mdekrey/raspberry-BB8/scad/my-bb8-glue-bracket.scad

include <my-bb8-config.scad>;

rotate([180, 0, 0])
translate([0,0, panelHeight - radius])
panelGlueBracket();
