mdekrey/raspberry-BB8/scad/my-bb8-overview.scad

include <my-bb8-config.scad>;

bodySphere();
head();
