mdekrey/raspberry-BB8/scad/my-bb8-panel-1.scad

include <my-bb8-config.scad>;

panel = 1;
translate([0,0, panelHeight - radius])
{
    toolPanel(panel);

    if ($preview) {
        panelRingQuarter(false);
    }
}
