mdekrey/raspberry-BB8/scad/my-bb8-panel-2.scad

include <my-bb8-config.scad>;

panel = 2;
translate([0,0, panelHeight - radius])
toolPanel(panel);
