mdekrey/raspberry-BB8/scad/my-bb8-panel-3.scad

include <my-bb8-config.scad>;

panel = 3;
translate([0,0, panelHeight - radius])
toolPanel(panel);
