mdekrey/raspberry-BB8/scad/my-bb8-panel-6.scad

include <my-bb8-config.scad>;

panel = 6;
translate([0,0, panelHeight - radius])
toolPanel(panel);
