mdekrey/raspberry-BB8/scad/my-bb8-ring-quarter.scad

include <my-bb8-config.scad>;

translate([0,0, panelHeight - radius])
panelRingQuarter(false);
