mdekrey/raspberry-BB8/scad/my-bb8-triangle-third.scad

include <my-bb8-config.scad>;

tFrameThird();
