mdekrey/raspberry-BB8/scad/my-bb8-triangle.scad

include <my-bb8-config.scad>;

echo("print dimensions: ");
echo(x = (cos(35) * radius), y = (cos(35) * radius), z = (cos(35) * radius));
tFrameTriangle();
