mdekrey/raspberry-BB8/scad/shared.scad

panelDegrees = 35; // https://rimstar.org/science_electronics_projects/bb-8_dimensions.htm
panelRadius = radius * sin(panelDegrees);
insertionTolerance = 0.3;

visibleBoltHole = 4 / 2;
visibleBoltOuterRadius = radius * 0.07734 / 2;
visibleBoltCoverRadius = visibleBoltOuterRadius / 2;
visibleBoltBezelDepth = visibleBoltOuterRadius * 0.2;
visibleBoltBezel = visibleBoltOuterRadius * 0.2;

panelRingDegrees = panelDegrees * 4/15;
panelRingInnerDegrees = panelDegrees - panelRingDegrees;
panelRingInnerRadius = radius * sin(panelRingInnerDegrees);
panelRingOuterOverlap = 3;
panelRingInnerOverlap = 1;
panelArmDegrees = panelDegrees * 0.6;
panelArmBoltDegrees = panelDegrees * 0.52;

if (camlockBoltRadius * 2 + 2 > camlockNutThickness)
    warn("Camlock Bolt/Nut sizes invalid");

panelLockBoltDegrees = 90/ringLocksPerQuadrant;
panelRadiusOffset = radius * cos(panelDegrees);
rotateLockDegrees = panelLockBoltDegrees * 0.6; // The number of degrees to rotate the lock
panelRotateLockOffset = (panelLockBoltDegrees - rotateLockDegrees) / 2; // The number of degrees offset from the start position for the initial lock

panelRingInnerActualDegrees = asin((panelRingInnerRadius - insertionTolerance) / radius);
panelRingInnerInternalDegrees = asin((panelRingInnerRadius + panelRingInnerOverlap - insertionTolerance)
    / (radius - wallThickness));
panelHeight = radius - cos(panelRingInnerInternalDegrees) * (radius - wallThickness);
ringThickness = cos(panelRingInnerActualDegrees) * radius - cos(panelRingInnerInternalDegrees) * (radius - wallThickness) - 0.8;

panelDesignDepth = radius - cos(asin((panelRingInnerRadius * 0.92) / radius)) * radius + insertionTolerance;
panelDesignRadius = wallThickness - 0.2 * millisPerInch;

headRadius = radius * 295/506;
headBaseHeight = 20 * headRadius / 147.5;
headConeHeight = 20 * headRadius / 147.5;
headConeRadius = 111.5 * headRadius / 147.5;
headOffset = cos(asin(headConeRadius / radius)) * radius;

module bodySphere(additionalWallThickness = 0) {
    difference() {
        sphere(radius, $fn=$fnBody);
        sphere(radius - wallThickness - additionalWallThickness, $fn=$fn);
    };
}

module panelRing() {
    intersection() {
        bodySphere(additionalWallThickness = cos(panelDegrees) * maxLip);

        difference() {
            union() {
                translate([0,0, (radius) * cos(panelDegrees) - wallThickness])
                cylinder(r=panelRadius - insertionTolerance - panelRingOuterOverlap, h=radius * 2);
                translate([0,0,radius + cos(panelDegrees) * radius])
                cube([(panelRadius - insertionTolerance + panelRingOuterOverlap) * 2, (panelRadius - insertionTolerance + panelRingOuterOverlap) * 2, radius * 2], center=true);
            }
            difference() {
                cylinder(r=panelRingInnerRadius, h=radius * 2);

                linear_extrude(height=radius)
                panelX();
            }

            intersection() {
                sphere(radius - wallThickness/2+insertionTolerance, $fn=$fn);
                cylinder(r=panelRingInnerRadius + panelRingInnerOverlap + insertionTolerance, h=radius);
            }
        }
    }

}

panelAdditionalWallThickness = 0; // cos(panelDegrees) * maxLip;
panelInnerWall = radius - wallThickness - panelAdditionalWallThickness;
panelLayerWall = radius - (radius - panelInnerWall) * 0.6;

module panelX(offset = 0) {
    for (arm=[0:90:359]) {
        rotate([0,0,arm+45])
        translate([-83, 83, 0])
        offset(r=offset)
        import("panel-x.svg", center=true, dpi=2611.8439045872/panelRingInnerRadius);
    }
}

module panel() {
    difference() {
        intersection() {
            bodySphere(additionalWallThickness = panelAdditionalWallThickness);

            union() {
                intersection() {
                    cylinder(r=panelRingInnerRadius - insertionTolerance, h=radius * 2);

                    difference() {
                        cube([radius*2,radius*2,radius*2], center=true);
                        sphere(radius - wallThickness/2 - insertionTolerance, $fn=$fn);

                        linear_extrude(height=radius)
                        panelX(offset=insertionTolerance);
                    }
                }

                intersection() {
                    sphere(radius - wallThickness/2 - insertionTolerance, $fn=$fn);
                    cylinder(r=panelRingInnerRadius + panelRingInnerOverlap - insertionTolerance, h=radius);
                }
            }

        }

        difference() {
            children();
            sphere(r=1);

            sphere(r=radius - panelDesignRadius, $fn=$fnDetail);
        }

        for (i = [0 : 90 : 360]) {
            rotate([0, panelArmBoltDegrees, i])
            translate([0, 0, radius - wallThickness - panelAdditionalWallThickness])
            rotate([0, 180, 0])
            visibleBoltHole();
        }
    }
}

module panelMain() {
    difference() {
        panel() children();

        if (smallPrintBed) {
            translate([
                0, 0,
                radius * 2 - panelHeight + ringThickness])
            rotate([0,0,90 + 20])
            translate([- insertionTolerance / 2, 0, 0])
            cube([insertionTolerance, radius*2, radius*2], center=true);
        }

        translate([
            0, 0,
            radius - panelHeight + ringThickness - insertionTolerance / 2])
        cube([radius*2, radius*2, insertionTolerance], center=true);


        if (smallPrintBed) {
            translate([
                0, 0,
                -panelHeight + ringThickness])
            linear_extrude(height=radius)
            for (i = [45,180 + 45])
            rotate([0,0,i])
            polygon([
                [+insertionTolerance / 2, +(panelRingInnerRadius + panelRingInnerOverlap)],
                [+insertionTolerance / 2, +(panelRingInnerRadius + panelRingInnerOverlap - 5)],
                [+insertionTolerance / 2 + 5, +(panelRingInnerRadius + panelRingInnerOverlap - 5)],
                [+insertionTolerance / 2 + 5, +(panelRingInnerRadius + panelRingInnerOverlap - 10)],
                [+insertionTolerance / 2, +(panelRingInnerRadius + panelRingInnerOverlap - 10)],
                [+insertionTolerance / 2, 0],
                [-insertionTolerance / 2, 0],
                [-insertionTolerance / 2, +(panelRingInnerRadius + panelRingInnerOverlap - 10 + insertionTolerance)],
                [-insertionTolerance / 2 + 5, +(panelRingInnerRadius + panelRingInnerOverlap - 10 + insertionTolerance)],
                [-insertionTolerance / 2 + 5, +(panelRingInnerRadius + panelRingInnerOverlap - 5 - insertionTolerance)],
                [-insertionTolerance / 2, +(panelRingInnerRadius + panelRingInnerOverlap - 5 - insertionTolerance)],
                [-insertionTolerance / 2, +(panelRingInnerRadius + panelRingInnerOverlap)],
            ]);
        }
    }
}

module panelDesign(panelNumber) {
    intersection() {
        difference() {
            resize(newsize = [panelRingInnerRadius*2,panelRingInnerRadius*2])
            import(str("tool-panel-",panelNumber,".svg"), center=true, dpi=200);

            rotate([0,0,45])
            panelX(insertionTolerance);
        }

        translate([panelRingInnerRadius*2 / 200, -panelRingInnerRadius*2 / 200])
        square([panelRingInnerRadius*2, panelRingInnerRadius*2], center=true);
    }
}

module panelDesignEmboss(panelDesign) {
        rotate(45)
        translate([0,0, radius - panelDesignDepth])
        linear_extrude(height=panelDesignDepth)
        offset(insertionTolerance)
        panelDesign(panelDesign);

}

module panelDesignCurved(panelDesign) {
    intersection() {
        rotate(45)
        translate([0,0, radius - panelDesignDepth + insertionTolerance])
        linear_extrude(height=panelDesignDepth)
        panelDesign(panelDesign);

        difference() {
            sphere(r=radius, $fn=$fnBody);
            sphere(r=radius - panelDesignRadius + insertionTolerance, $fn=$fnDetail);
        }
    }
}

module tFrame() {
    difference() {
        bodySphere();

        rotate([90, 0, 0])
        cylinder(r1=panelRadius - panelRingOuterOverlap, r2=panelRadius - panelRingOuterOverlap, h=radius * 2, center=true);
        rotate([0, 90, 0])
        cylinder(r1=panelRadius - panelRingOuterOverlap, r2=panelRadius - panelRingOuterOverlap, h=radius * 2, center=true);
        cylinder(r1=panelRadius - panelRingOuterOverlap, r2=panelRadius - panelRingOuterOverlap, h=radius * 2, center=true);

        translate([0,0,radius + cos(panelDegrees) * radius - insertionTolerance])
        cube([(panelRadius + panelRingOuterOverlap) * 2, (panelRadius + panelRingOuterOverlap) * 2, radius * 2], center=true);

        rotate([-90, 0, 0])
        translate([0,0,radius + cos(panelDegrees) * radius - insertionTolerance])
        cube([(panelRadius + panelRingOuterOverlap) * 2, (panelRadius + panelRingOuterOverlap) * 2, radius * 2], center=true);

        rotate([0, 90, 0])
        translate([0,0,radius + cos(panelDegrees) * radius - insertionTolerance])
        cube([(panelRadius + panelRingOuterOverlap) * 2, (panelRadius + panelRingOuterOverlap) * 2, radius * 2], center=true);
    }
}

module tFrameTriangle() {
    rotationDifference = 30.5;
    difference() {
        intersection() {
            polyhedron(
            points=[ [0,0,2*radius],[2*radius,0,0],[0,2*radius,0], // the three points at base
                    [0,0,0]  ],                                 // the apex point
            faces=[ [0,1,3],[1,2,3],
                        [2,0,3],[2,1,0] ]
            );

            tFrame();
        }

        // interlocking holes for other frame triangles
        // when facing from the outside, bottom, left, right
        for (rotationAxis = [[0,0,0],[1,0,0],[0,-1,0]])
            rotate(90, rotationAxis)
            for (interlock = [-5, 5])
                rotate([0,-90,45 + interlock])
                translate([0,0,-(radius - wallThickness - 0)])
                rotate([0,0,90])
                camLockSlot(boltLength=camlockBoltLength);

        // outer-ring holes - when facing from the outside, left, right, top
        for (side = [[0,-90,0], [90,0,0], [180,0,90]])
            for (position = [panelLockBoltDegrees:panelLockBoltDegrees:89])
                rotate(side)
                rotate([0,0,-position])
                rotate([panelDegrees,0,0])
                translate([0,0,-(radius - wallThickness - 0)])
                camLockSlot(boltLength=camlockBoltLength);
        // end outer-ring holes

        // visible bolt-hole covers (bottom, left, right)
        for (rotationAxis = [[0,0,0],[1,0,0],[0,-1,0]])
            rotate(45, rotationAxis)
            rotate(45, [0, 0, 1])
            rotate(90-35/2, [0, 1, 0])
            translate([0, 0, radius])
            outerWallBoltHole();

    }
}

module tFrameThird() {
    rotationDifference = 30.5;
    difference() {
        intersection() {
            polyhedron(
            points=[ [radius,radius,radius],[2*radius,0,0],[0,2*radius,0], // the three points at base
                    [0,0,0]  ],                                 // the apex point
            faces=[ [0,1,3],[1,2,3],
                        [2,0,3],[2,1,0] ]
            );

            tFrame();
        }

        // bottom holes
        rotate([0,-90,40])
        translate([0,0,-(radius - wallThickness - 0)])
        rotate([0,0,90])
        camLockSlot(boltLength=camlockBoltLength);

        rotate([0,-90,50])
        translate([0,0,-(radius - wallThickness - 0)])
        rotate([0,0,90])
        camLockSlot(boltLength=camlockBoltLength);

        // adjacent tri holes
        for (camlockOffset = [adjacentCamlockOffsetStart:adjacentCamlockOffsetStep:adjacentCamlockOffsetMax]) {
            rotate(a=-camlockOffset - panelDegrees, v=[-1,0,1])
            rotate([0,-90,90])
            translate([0,0,-(radius - wallThickness - 0)])
            rotate([0,0,-45 + rotationDifference]) // bolt rotation
            camLockSlot(boltLength=camlockBoltLength);

            rotate(a=-camlockOffset - panelDegrees, v=[-1,0,1])
            rotate([0,-90,90])
            translate([0,0,-(radius - wallThickness - 0)])
            rotate([0,0,-45 - rotationDifference]) // bolt rotation
            camLockSlot(boltLength=camlockBoltLength);

            rotate(a=camlockOffset + panelDegrees, v=[0,-1,1])
            rotate([0,-90,0])
            translate([0,0,-(radius - wallThickness - 0)])
            rotate([0,0,-135 + rotationDifference]) // bolt rotation
            camLockSlot(boltLength=camlockBoltLength);

            rotate(a=camlockOffset + panelDegrees, v=[0,-1,1])
            rotate([0,-90,0])
            translate([0,0,-(radius - wallThickness - 0)])
            rotate([0,0,-135 - rotationDifference]) // bolt rotation
            camLockSlot(boltLength=camlockBoltLength);
        }

        // outer-ring holes
        // TODO: change this first param to offset with panelLockBoltDegrees*0.5
        for (position = [panelLockBoltDegrees:panelLockBoltDegrees:44]){
            rotate([0,-90,0])
            rotate([0,0,-position])
            rotate([panelDegrees,0,0])
            translate([0,0,-(radius - wallThickness - 0)])
            rotate([0,0,180]) // bolt rotation
            camLockSlot(boltLength=camlockBoltLength);

            rotate([90,0,0])
            rotate([0,0,-position -45])
            rotate([panelDegrees,0,0])
            translate([0,0,-(radius - wallThickness - 0)])
            rotate([0,0,180]) // bolt rotation
            camLockSlot(boltLength=camlockBoltLength);
        }
        // end outer-ring holes

        // visible bolt-hole cover
        rotate([0, 90 - 35 / 2, 45])
        translate([0, 0, radius])
        visibleBoltHole();

        rotate([0, 90 - 35 / 2, 45])
        translate([0, 0, radius - wallThickness])
        rotate([180, 0, 0])
        visibleBoltHole();
    }
}

module panelRingQuarter(split = false) {
    panelRingCenterDegrees = (panelDegrees - panelRingDegrees / 2);
    endHoleOffset = 180-panelDegrees + panelRingDegrees *0.625;
    quarterRingRotation = -(panelLockBoltDegrees+panelRotateLockOffset+rotateLockDegrees);
    difference() {
        intersection() {
            rotate([0,0,quarterRingRotation])
            translate([insertionTolerance*0.5,insertionTolerance*0.5,0])
            cube([radius, radius, radius]);

            panelRing();
        }

        rotate([0,0,quarterRingRotation])
        {
            // end holes
            for (end = [-1 : (split ? 1 : 2) : 1]) {
                rotate([endHoleOffset,0,-45 + 45 * end])
                translate([0,0,-(radius - camlockNutThickness)])
                rotate([0,90,0]) // bolt rotation
                cylinder(r=pinRadius + insertionTolerance / 2, h=pinLength + insertionTolerance, center=true);
            }

            // rotate lock holes
            for(loop = [panelRotateLockOffset : panelLockBoltDegrees : 90]) {
                // The hole in line with the panel arm does not exist to ensure proper alignment of the pieces
                if (loop != panelRotateLockOffset + panelLockBoltDegrees) {
                    rotate([0,0,loop])
                    translate([0,0, radius * cos(panelDegrees)])
                    rotateLockSlot(boltLength=camlockBoltLength, radius = panelRadius, angle = rotateLockDegrees, downwardAngle = panelDegrees);
                }
            }

            // visible bolt
            // TODO: the arm and bolt should line up with the lock hole, regardless of the number of bolts
            rotate([0, panelArmBoltDegrees, 15+panelRotateLockOffset+rotateLockDegrees])
            translate([0, 0, radius])
            rotate([0, 0, 0])
            visibleBoltHole();
        }
    }
}


module panelGlueBracket() {
    panelRingCenterDegrees = (panelDegrees - panelRingDegrees / 2);
    endHoleOffset = 180-panelDegrees + panelRingDegrees *0.625;
    difference() {
        translate([panelRingInnerRadius - 20,0,radius - panelHeight / 2])
        cube([60, 40, panelHeight], center=true);

        translate([panelRingInnerRadius + 10,0,radius - panelHeight / 2])
        scale([0.6,1,1])
        rotate([0,0,45])
        cube([5, 5, panelHeight+1], center=true);

        translate([panelRingInnerRadius + 10,0,radius - panelHeight / 2])
        scale([0.6,1,1])
        rotate([0,45,0])
        cube([5, 40+1, 5], center=true);

        translate([0,0,1])
        difference() {
            cylinder(r=panelRingInnerRadius, h=radius);

            rotate([0,0,-45])
            linear_extrude(height=radius)
            import("panel-x.svg", center=true, dpi=2611.8439045872/panelRingInnerRadius);

        }

        intersection() {
            sphere(radius - wallThickness/2+insertionTolerance, $fn=$fn);
            cylinder(r=panelRingInnerRadius + panelRingInnerOverlap + insertionTolerance, h=radius);
        }

        // visible bolt
        rotate([0, panelArmBoltDegrees, 0])
        translate([0, 0, radius + wallThickness])
        rotate([0, 0, 0])
        translate([0, 0, -wallThickness * 2])
        cylinder(r = visibleBoltHole, h=wallThickness * 5, $fn=$fn);
    }
}

module rotateLockSlot(boltLength, radius, angle, downwardAngle) {
    offset = -wallThickness + camlockNutThickness * 0.5;
    yOffset = offset * cos(downwardAngle);
    xOffset = offset * sin(downwardAngle);
    translate([0,0,yOffset])
    union() {
        hull() {
            rotate([0,90,angle])
            translate([0, 0, radius+xOffset])
            rotate([0,downwardAngle,0])
            cylinder(r=(camlockBoltRadius + insertionTolerance / 2), h=boltLength, center=true, $fn=$fnDetail);

            rotate([0,90,0])
            translate([0, 0, radius+xOffset])
            rotate([0,downwardAngle,0])
            cylinder(r=(camlockBoltRadius + insertionTolerance / 2), h=boltLength, center=true, $fn=$fnDetail);

            rotate_extrude(angle = angle, $fn=$fnDetail) {
                translate([radius+xOffset,0])
                rotate(-downwardAngle)
                translate([- boltLength/2, -(camlockBoltRadius + insertionTolerance / 2)])
                square([boltLength, 2*(camlockBoltRadius + insertionTolerance / 2)]);
            }
        }

        rotate([0,90,0])
        translate([0, 0, radius+xOffset])
        rotate([0,downwardAngle,0])
        translate([(camlockBoltRadius + insertionTolerance / 2) + wallThickness/2, 0, 0])
        cube([(camlockBoltRadius + insertionTolerance / 2)*2 + wallThickness,(camlockBoltRadius + insertionTolerance / 2)*2, boltLength], center=true);
    }
}

module camLockSlot(boltLength) {
    translate([0,-boltLength/2,0])
    rotate([180, 0, 0])
    union() {
        translate([0,0,-camlockNutMaxDepth])
        cylinder(r1=camlockNutRadius, r2=camlockNutRadius, h=camlockNutThickness + camlockNutMaxDepth, $fn=$fn);

        translate([0,-boltLength,-camlockNutMaxDepth])
        cylinder(r1=camlockNutRadius, r2=camlockNutRadius, h=camlockNutThickness + camlockNutMaxDepth, $fn=$fn);

        rotate([90,0,0])
        translate([0, camlockNutThickness * 0.5, 0])
        cylinder(r1=(camlockBoltRadius + insertionTolerance / 2), r2=(camlockBoltRadius + insertionTolerance / 2), h=boltLength);
    }
}

module visibleBoltHole() {
    translate([0, 0, -visibleBoltBezelDepth])
    cylinder(r1=visibleBoltOuterRadius - visibleBoltBezel * 2, r2=visibleBoltOuterRadius, h=visibleBoltBezelDepth * 2, $fn=$fnDetail);

    translate([0, 0, -wallThickness * 2])
    cylinder(r = visibleBoltHole, h=wallThickness * 2, $fn=$fn);
}

module outerWallBoltHole() {
    // front inset
    translate([0, 0, -visibleBoltBezelDepth])
    cylinder(r1=visibleBoltOuterRadius - visibleBoltBezel * 2, r2=visibleBoltOuterRadius, h=visibleBoltBezelDepth * 2, $fn=$fnDetail);

    translate([0, 0, -wallThickness * 2])
    cylinder(r = visibleBoltHole, h=wallThickness * 2, $fn=$fn);

    // back inset
    translate([0, 0, - wallThickness])
    rotate([180, 0, 0])
    translate([0, 0, -visibleBoltBezelDepth])
    cylinder(r1=visibleBoltOuterRadius - visibleBoltBezel * 2, r2=visibleBoltOuterRadius, h=visibleBoltBezelDepth * 2, $fn=$fnDetail);
}

module toolPanel(panel) {
    if (panel == 0)
        panelMain();
    else {
        panelMain()
        union()
        {
            panelDesignEmboss(panel);
            panelCutout(panel);
        }
        panelDesignCurved(panel);
    }
}

module panelCutout(panel) {
    if (panel != 3 && panel != 4) {
        intersection() {
            if (panel != 2)
            panelDesignEmboss(str(panel, "-cutout"));

            if (panel == 1) {
                intersection() {
                    union() {
                    rotate([0,0,-45])
                    translate([0,0, radius + 2.5])
                    for (i = [0:1 / 30 :1]) {
                    rotate([0,0,i * 360])
                    rotate(-10, v = [1,-1,0])

                    linear_extrude(height=10)
                    intersection() {
                        circle(r=60);
                        square([60,60]);
                    }
                    }
                    }
                }
            }
            if (panel == 5) {
                union() {

                    translate([0,-36, radius - 2.75])
                    rotate([8,0,0])
                    scale([1,1,1/15.5])
                    sphere(r=15.5);

                    depth = 1;
                    intersection() {
                        union() {
                        rotate([0,0,-45])
                        translate([0,0, radius + 2.5])
                        for (i = [0:1 / 15 :1]) {
                        translate([0,0,i * 1])
                        rotate([0,0,i * 180])
                        rotate(-10, v = [1,-1,0])

                        linear_extrude(height=10)
                        intersection() {
                            circle(r=60);
                            square([60,60]);
                        }
                        }
                        }

                        rotate([0,0,45])
                        translate([-60, 0, radius - panelDesignDepth])
                        cube([120, 60, radius]);
                    }
                }
            }
            if (panel == 2) {
                union() {
                    rotate([0, 11.193381591600671, 45 + 79.94651307773178])
                    translate([0, 0, radius - 6])
                    difference() {
                        cylinder(r=radius * sin(3.2278906006438186) + insertionTolerance, h=panelDesignDepth * 2);
                        translate([0,0,insertionTolerance])
                        cylinder(r=radius * sin(3.2278906006438186), h=panelDesignDepth * 2);
                    }


                    rotate([0, 4.210262618975445, 45 + 33.815798010531786])
                    translate([0, 0, radius])
                    scale([1,1, 1 / (radius * sin(3.2278906006438186))])
                    sphere(r=radius * sin(3.2278906006438186));
                }
            }
        }
    }
}

module head()
{
    translate([0,0, headOffset])
    {
        translate([0,0, headBaseHeight + headConeHeight])
        intersection() {
            difference(){
                sphere(headRadius, $fn=$fnBody);

                // make the head hollow.
                // start with a cylinder at the base so the bolts can be added
                translate([0,0,-insertionTolerance])
                cylinder(camlockBoltLength * 0.6 + insertionTolerance*2, headRadius-wallThickness, headRadius-wallThickness, $fn=$fnBody);
                // make the top half of the head hollow; keep it a cone so that it doesn't need supports
                translate([0,0,-insertionTolerance + camlockBoltLength * 0.6])
                cylinder(headRadius-camlockBoltLength * 0.6-wallThickness, headRadius-wallThickness, 0, $fn=$fnBody);
            }
            // Just the top half
            translate([-headRadius, -headRadius, 0])
            cube([headRadius*2, headRadius*2, headRadius]);
        }

        // The base has a portion that is purely a cylinder
        translate([0,0, headConeHeight])
        difference() {
            cylinder(headBaseHeight, headRadius, headRadius, $fn=$fnBody);

            translate([0,0, - insertionTolerance])
            cylinder(headBaseHeight + insertionTolerance*2, headRadius - wallThickness, headRadius - wallThickness, $fn=$fnBody);
        }

        // ... followed by a cone that comes down to the base itself
        difference() {
            cylinder(headConeHeight, headConeRadius, headRadius, $fn=$fnBody);

            // And hollow out the cone, but end in a cylinder so we don't have a sharp edge
            translate([0,0, - insertionTolerance])
            cylinder(headBaseHeight + insertionTolerance*2, headConeRadius - wallThickness, headRadius - wallThickness, $fn=$fnBody);
            translate([0,0, - insertionTolerance])
            cylinder(headBaseHeight + insertionTolerance*2, headConeRadius - wallThickness * 0.1, headConeRadius - wallThickness * 0.1, $fn=$fnBody);
        }
    }
}

module headDetail()
{
    difference()
    {
        head();

        // horizontal slice at the decoration part so that we can print the inside cleanly and keep all overhangs inside, too
        translate([
            0, 0,
            headOffset + headConeHeight + headBaseHeight])
        cube([headRadius*2, headRadius*2, insertionTolerance], center=true);

        for (ring = [0.1,0.9])
        translate([
            0, 0,
            headOffset + headConeHeight + headBaseHeight * ring])
        difference() {
            cylinder(headBaseHeight * 0.1, headRadius+5, headRadius+5);
            cylinder(headBaseHeight * 0.2, headRadius - wallThickness / 10, headRadius - wallThickness / 10);
        }

        for (outerBolt = [0 : 45 : 360]) {
            rotate([0,0,outerBolt])
            translate([0, headRadius - wallThickness, headOffset + headConeHeight + headBaseHeight])
            rotate([90,0,0])
            camLockSlot(boltLength=camlockBoltLength);
        }
    }
}

module warn(text)
{
    echo(str("<span style='background-color: #ffffb0'>", text, "</span>"));
}
